frezik/bodgery_rfid/power_adaptor/power_adaptor.sch

## KiCad design power_adaptor/power_adaptor.sch (2014-12-29)

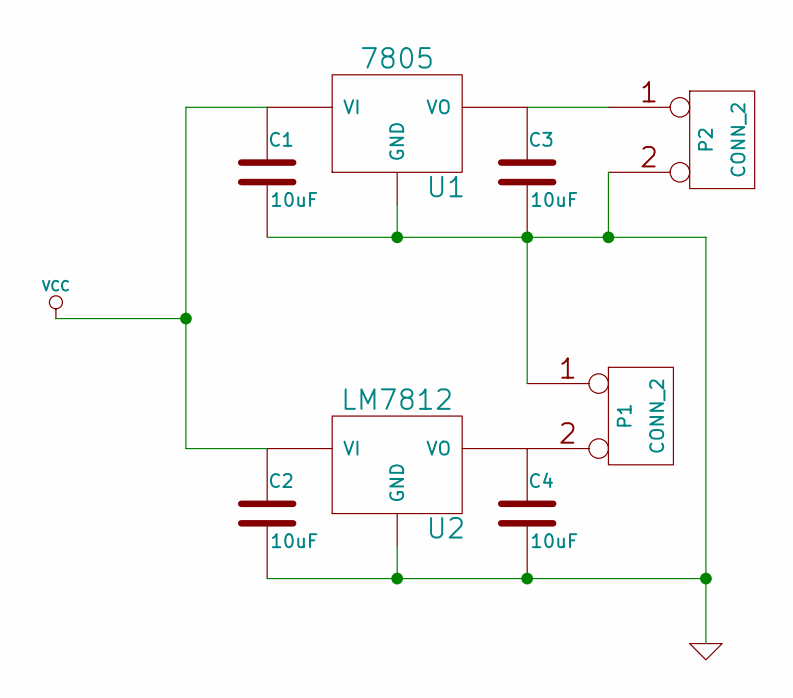
[picture p4: schematic power_adaptor.sch]

Parts:
C1, C2, C3, C4: 10uF
P1, P2: CONN_2
U1: 7805
U2: LM7812

Connections:
GND: C1.2, C2.2, C3.2, C4.2, P1.1, P2.2 (PM), U1.GND, U2.GND
unnamed: C3.1, P2.1, U1.VO
unnamed: C4.1, P1.2 (PM), U2.VO
VCC: C1.1, C2.1, U1.VI, U2.VI
